rickcox/Hexa-Pi/Hexa-Pi_PCB/doc/Hexa-Pi_1.1_BARE_TOP.png

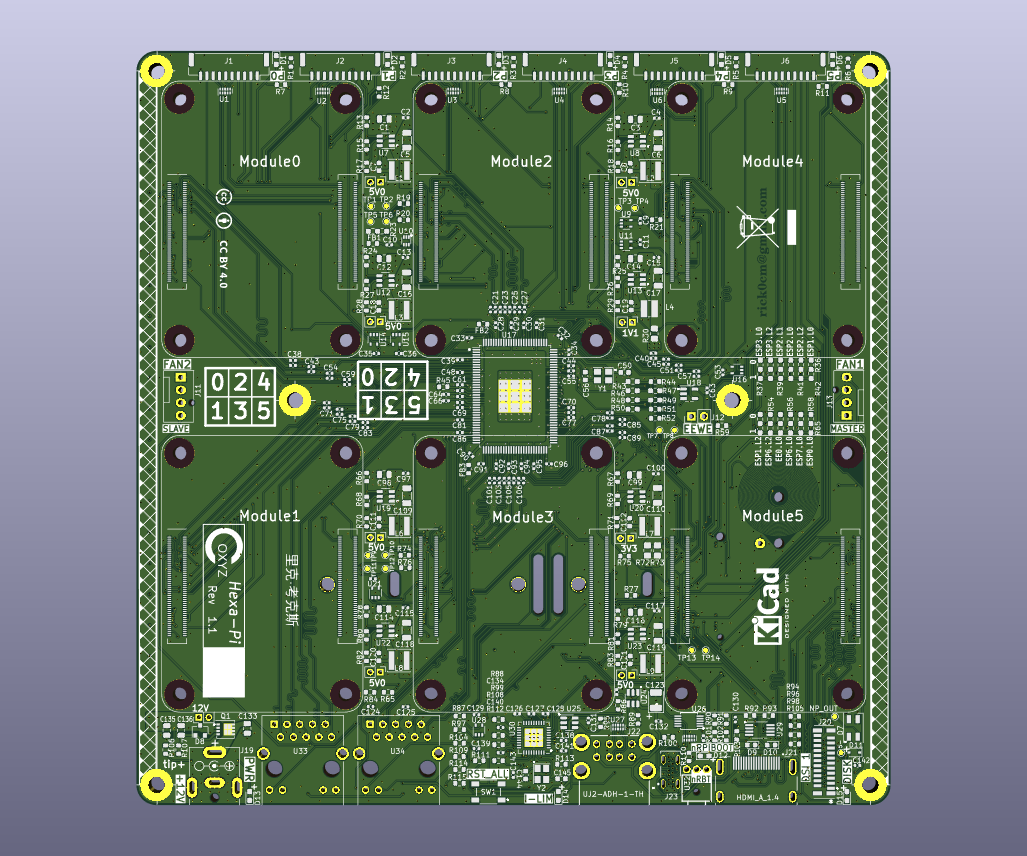
Hexa-Pi_PCB/doc/Hexa-Pi_1.1_BARE_TOP.png
